m24h/ESP8266ADDA/circuit/output/3d.png

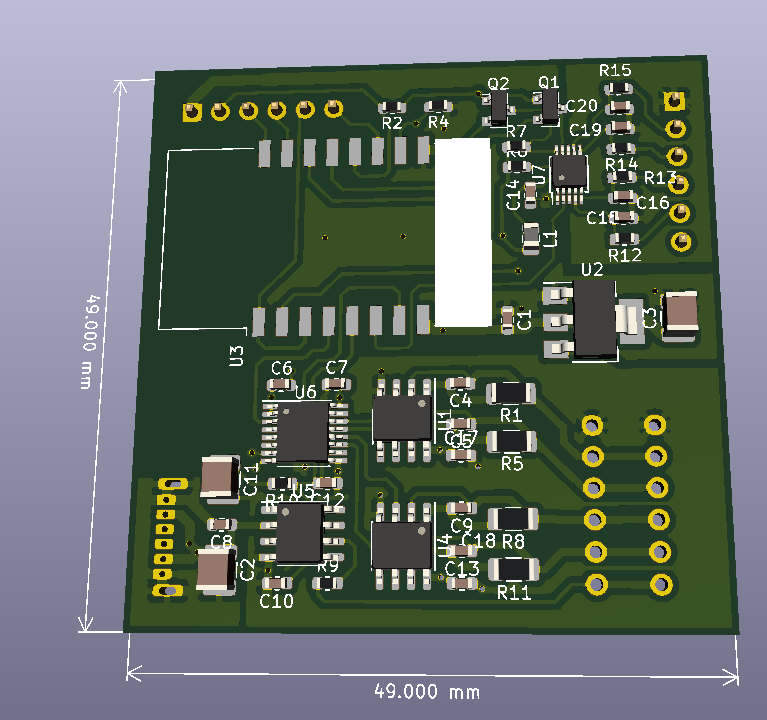
circuit/output/3d.png
