m24h/ESP8266ADDA/circuit/output/pcb_b.png

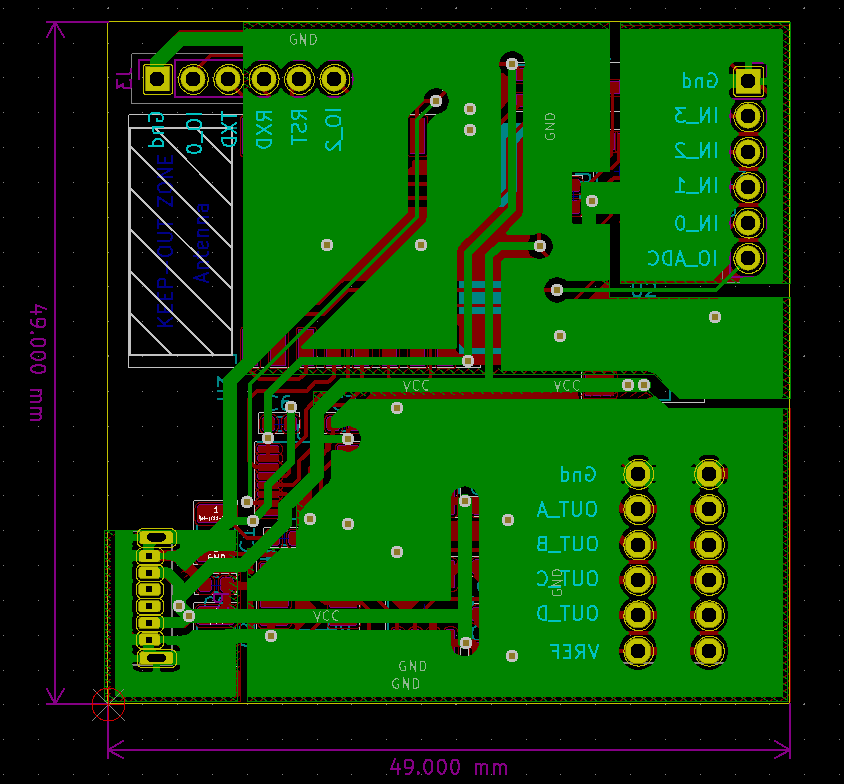
circuit/output/pcb_b.png
