m24h/ESP8266ADDA/circuit/output/pcb_f.png

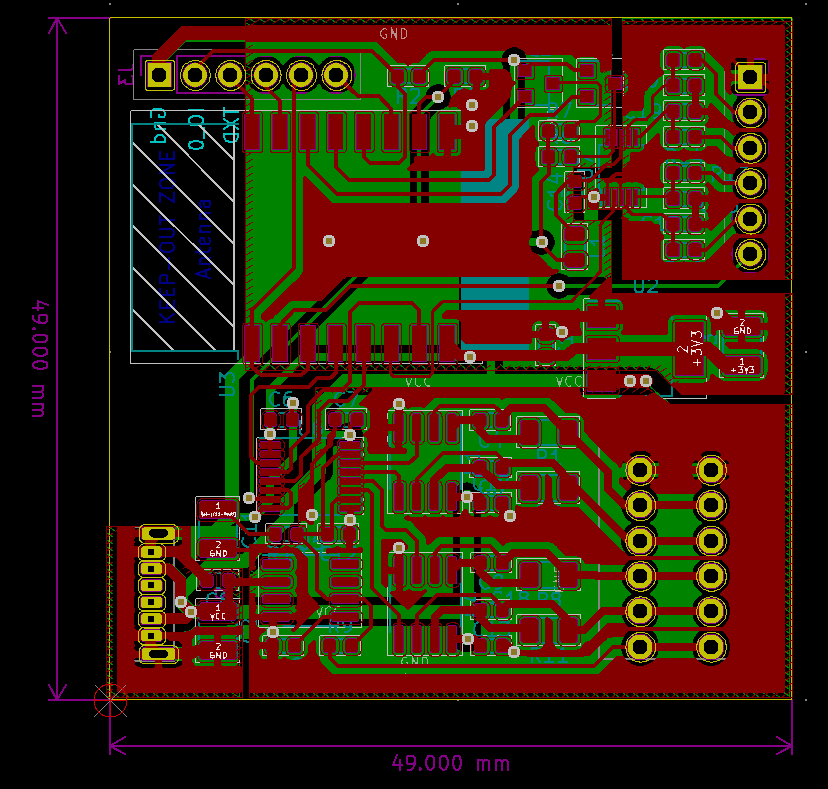
circuit/output/pcb_f.png
