m24h/ESP8266ADDA/circuit/output/sch.png

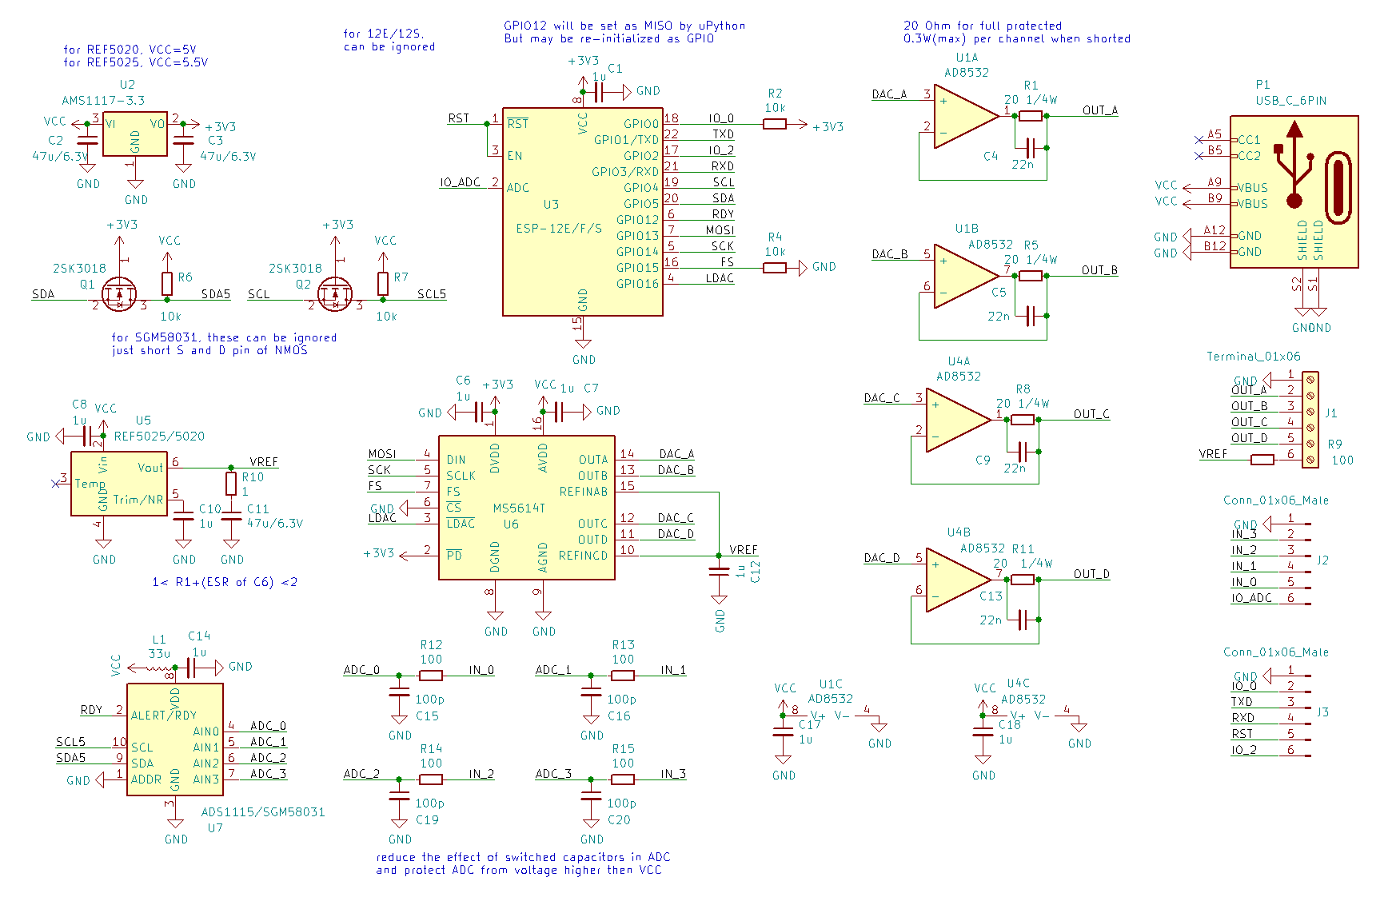
circuit/output/sch.png
