m24h/ESP8266ADDA/practice/CV-CuSo4-Measuring.jpg

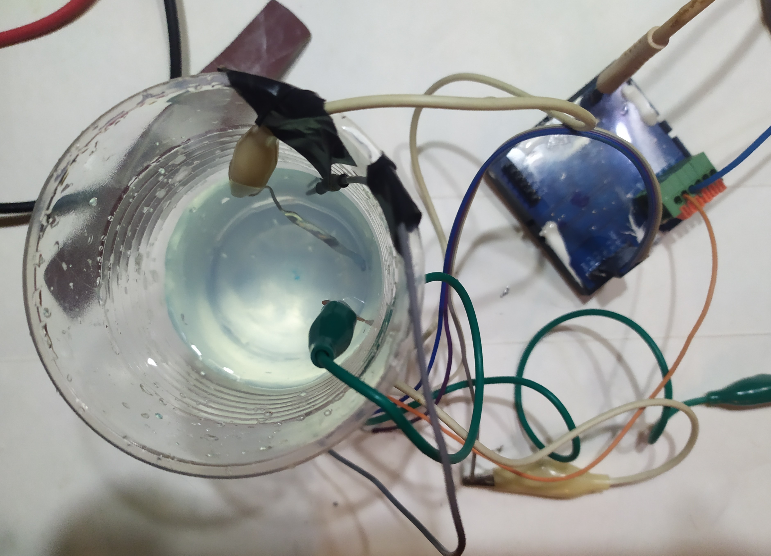
practice/CV-CuSo4-Measuring.jpg
