m24h/ESP8266ADDA/practice/finished.jpg

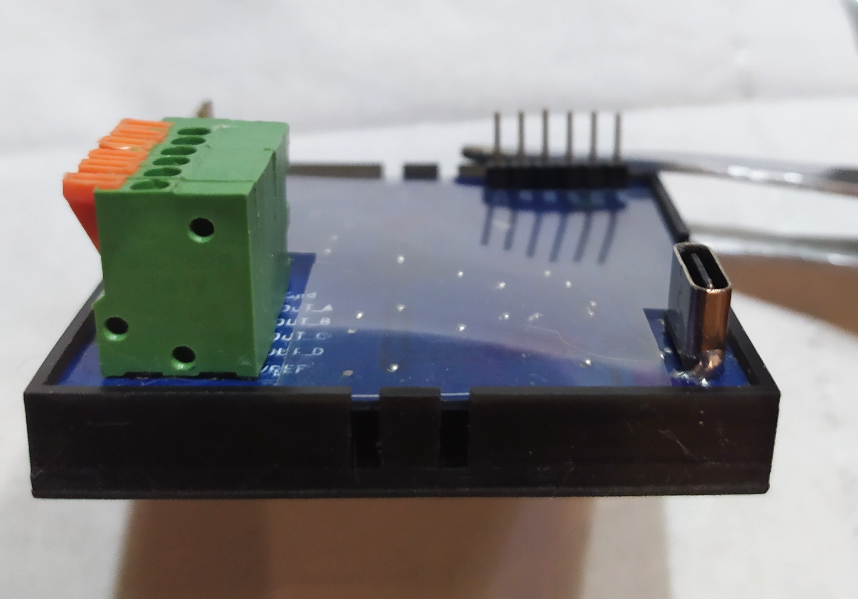
practice/finished.jpg
