m24h/ESP8266ADDA/practice/pcb1.jpg

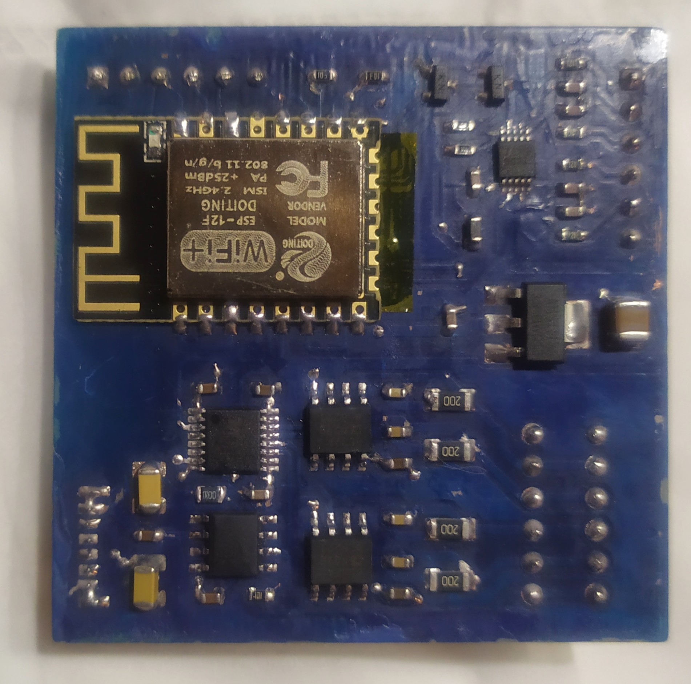
practice/pcb1.jpg
