m24h/ESP8266ADDA/practice/pcb2.jpg

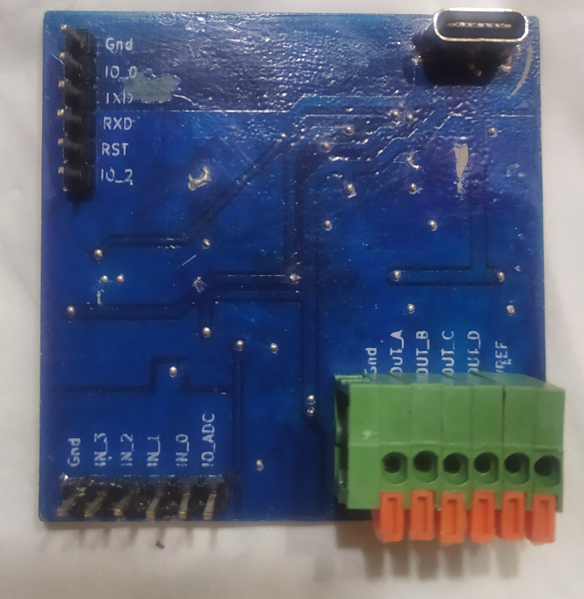
practice/pcb2.jpg
