m24h/ESP8266ADDA/practice/sheild.jpg

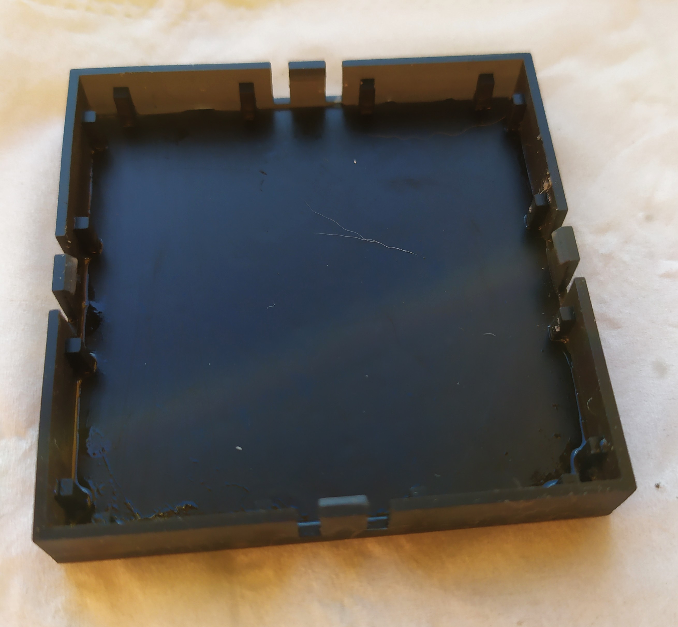
practice/sheild.jpg
