m24h/ESP8266ADDA/code/on_pc/info.py

import arpc
import asyncio
import conf

import binascii

async def info():
	async with await arpc.connect(conf.server['host'], conf.server['port'], password=conf.server['password']) as sess:
		await sess.exec('import sys')
		print('sys.implementation : ', await sess.eval('repr(sys.implementation)')) # now json.dumps can dump sys.implementation incorrectly, but fails when loads() it
		await sess.exec('import machine')
		print('machine.freq :', await sess.eval('machine.freq()'))
		print('machine.unique_id :', binascii.hexlify((await sess.eval('machine.unique_id()')).encode('iso8859-1')).decode('iso8859-1'))
		await sess.exec('import os')
		print('disk free :', await sess.eval('(s:=os.statvfs("/")) and s[0]*s[3]'))
		await sess.exec('import gc\ngc.collect()')
		print('gc.mem_free :', await sess.eval('gc.mem_free()'))
		print('gc.mem_alloc :', await sess.eval('gc.mem_alloc()'))
		await sess.exec('import micropython')
		print('micropython.stack_use :', await sess.eval('micropython.stack_use()'))
		print('RPC :', await sess.list())
		print('hw_id :', await sess.hw_id())
		try:
			print('app_id :', await sess.app_id())
		except:
			pass
		print('help :')
		print('\t'+(await sess.help()).replace('\n','\n\t'))


if __name__=='__main__':
	asyncio.run(info())
