m24h/ESP8266ADDA/code/on_pc/reset.py

import arpc
import asyncio
import conf

async def cmds():
	async with await arpc.connect(conf.server['host'], conf.server['port'], password=conf.server['password']) as sess:
		await sess.exec('''
print('Reset ...')
import machine
machine.reset()
''', __arpc_toss=True)

if __name__=='__main__':
	asyncio.run(cmds())
